isand3r/openOBD/hardware/schematics/first_prototype.sch

## EAGLE design hardware/schematics/first_prototype.sch (2016-11-15)

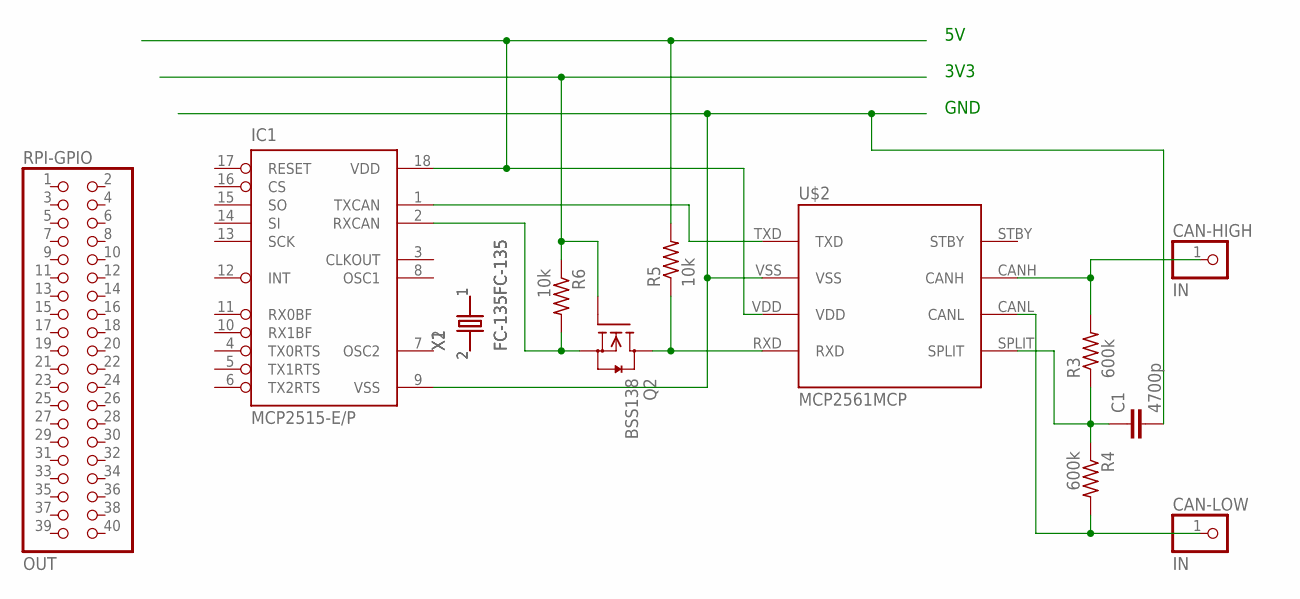
[picture p47: schematic first_prototype.sch]

Parts:
C1: 4700p; C2.5-2
CAN-HIGH: IN; 1X01
CAN-LOW: IN; 1X01
IC1: MCP2515-E/P; DIL18
Q2: BSS138; SOT23
R3, R4: 600k; M2309
R5, R6: 10k; M2309
RPI-GPIO: OUT; 2X20
U$2: MCP2561MCP; MCP2561_PDIP
X1, X2: FC-135FC-135; FC-135

Connections:
unnamed: Q2.1 (G), R6.1
unnamed: C1.2, IC1.9 (VSS), U$2.VSS
unnamed: C1.1, R3.1, R4.1, U$2.SPLIT
unnamed: CAN-HIGH.1, R3.2, U$2.CANH
unnamed: CAN-LOW.1, R4.2, U$2.CANL
unnamed: IC1.2 (RXCAN), Q2.2 (S), R6.2
unnamed: Q2.3 (D), R5.1, U$2.RXD
unnamed: X1.2, X2.2
unnamed: X1.1, X2.1
unnamed: IC1.18 (VDD), R5.2, U$2.VDD
unnamed: IC1.1 (TXCAN), U$2.TXD

Notes on the sheet:
3V3
GND
